CoolNamesAllTaken/scbs/solidworks/fab/enclosure_parts.3mf

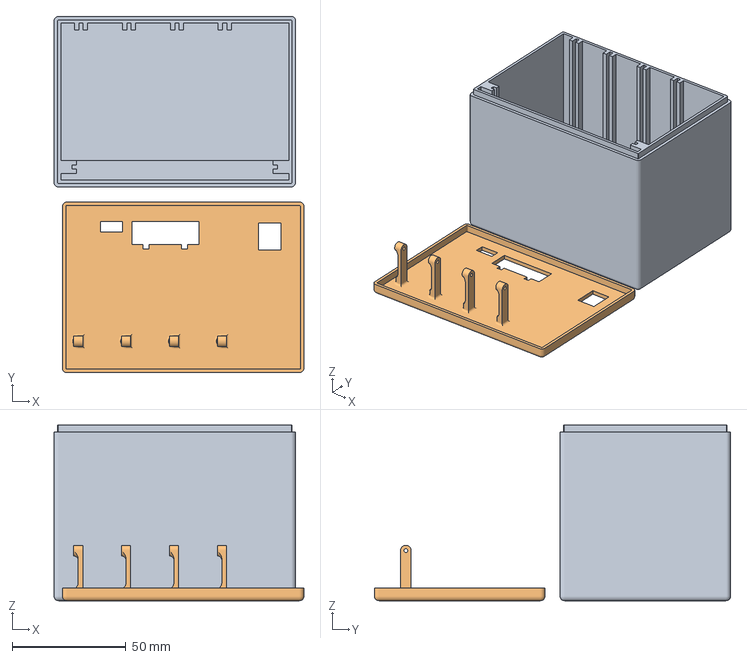
[picture p12: CAD file, 2022-12-04]
solidworks/fab/enclosure_parts.3mf
109.7 x 156.3 x 77.0 mm
enclosure_back_shell.STL
enclosure_front_panel.STL
