CoolNamesAllTaken/scbs/ltspice/cmd_pwm_tran.asc

C1: cap; 0.1µ
C2: cap; 0.1µ
Q1: npn; 2N3904
Q2: npn; 2N3904
R1: res; 10k
R2: res; 100
R3: res; 10k
R4: res; 10k
R5: res; 2k
R6: res; 10k
R7: res; 100
R8: res; 10k
V1: voltage; 5
V2: voltage; PULSE(0 3.3 0 1n 1n 10u 20u)
V3: voltage; PULSE(0 3.3 0 1n 1n 10u 20u)
Named nets: 0, 5v
.tran 10m
