CoolNamesAllTaken/scbs/ltspice/diff_amp_sim_ac.asc

C1: cap; 0.1µ
C4: cap; 0.1µ
C5: cap; 1µ
Q1: npn; 2n3904
Q2: pnp; 2n3906
R1: res; 1k
R2: res; 1k
R4: res; 10k
R5: res; 1
R6: res; 25
R7: res; 500k
R8: res; 500k
R9: res; 8.25Meg
R10: res; 8.25Meg
R11: res; 10k
R12: res; 100
R13: res; 10k
R14: res; 1
U1: UniversalOpAmp3
U2: UniversalOpAmp2
V1: voltage; 5
V2: voltage; 0; AC 1
V3: voltage; 3
Named nets: 0, 5v, out, csense, up, dn, fb, inm, hello
Q1 inverts ouptut polarity
and provides base drive for
.ac dec 1000 1m 1G
