CoolNamesAllTaken/scbs/ltspice/diff_amp_sim_offset_tran.asc

C1: cap; 1µ
C2: cap; 10n
C3: cap; 0.1µ
C4: cap; 0.1µ
Q1: npn; 2n3904
Q2: pnp; 2n2907
R1: res; 1k
R2: res; 1k
R3: res; 10k
R4: res; 2k
R5: res; 1
R6: res; 22.5
R7: res; 500k
R8: res; 500k
R9: res; 8.25Meg
R10: res; 8.25Meg
R11: res; 1
R12: res; 100
R13: res; 10k
R14: res; 2k
R15: res; 10k
U1: UniversalOpAmp2; Avol=10k GBW=10Meg Slew=18Meg
U2: UniversalOpAmp2
V1: voltage; 5
V2: voltage; SINE(2.25 2.25 100)
V3: voltage; PULSE(0 4.5 0 1n 1n 50m 100m)
V4: voltage; 3m
V5: voltage; 3m
Named nets: 0, 5v, out, csense, up, dn, cmd, hello
Q1 inverts ouptut polarity
and provides base drive for
.tran 0 100m 0 1u
