CoolNamesAllTaken/scbs/ltspice/idea_sim.asc

C1: cap; 0.1µ
R1: res; 100k
R3: res; 100
U1: LT1117
U2: UniversalOpAmp2
V1: voltage; 5
V2: voltage; PULSE(0 3.3 0 10m 0 10m 50m)
Named nets: 0, 5v, out, ref, cmd
.tran 0 10m 0 1u
V(out)-V(ref) = 1.25V
V(out) = V(ref) * (1 + R2/R1) + I(adj)*R2
