CoolNamesAllTaken/scbs/ltspice/npn_output_sim.asc

Q1: npn; 2n3904
R1: res; 10
U1: UniversalOpAmp2
V1: voltage; 5
V2: voltage; PULSE(0 4.5 0 10m 0 10m 50m)
Named nets: 0, cmd, 5v
.tran 0 10m 0 1u
V(out)-V(ref) = 1.25V
V(out) = V(ref) * (1 + R2/R1) + I(adj)*R2
