CoolNamesAllTaken/scbs/ltspice/rail_output_sim.asc

2n3906: pnp
C1: cap; 0.1µ
Q1: npn; 2n3904
R1: res; 1k
R2: res; 100
R3: res; 14.24k
R4: res; 10k
U1: UniversalOpAmp2
V1: voltage; 5
V2: voltage; SINE(1.65 1.65 10k 0 0)
Named nets: 0, cmd, 5v
.tran 0 1m 0
V(out)-V(ref) = 1.25V
V(out) = V(ref) * (1 + R2/R1) + I(adj)*R2
