CoolNamesAllTaken/scbs/ltspice/rail_output_sim_ac.asc

C1: cap; 0.1µ
C2: cap; 1p
C3: cap; 0.1µ
C4: cap; 10µ
Q1: npn; 2n3904
Q2: pnp; 2n3906
R1: res; 1k
R2: res; 1k
R3: res; 100k
R4: res; 100k
R5: res; 1
R6: res; 25
R7: res; 500k
R8: res; 500k
R9: res; 8.25Meg
R10: res; 8.25Meg
R12: res; 100
R13: res; 10k
U1: UniversalOpAmp3
U2: UniversalOpAmp2
V1: voltage; 5
V2: voltage; 0; AC 1
V3: voltage; 3
Named nets: 0, 5v, out, csense, up, dn, fb, inm
Q1 inverts ouptut polarity
and provides base drive for
.ac dec 1000 1m 10Meg
