CoolNamesAllTaken/scbs/ltspice/rail_output_sim_tran.asc

C1: cap; 1µ
C2: cap; 1p
C3: cap; 0.1µ
C4: cap; 10n
C5: cap; 10µ
Q1: npn; 2n3904
Q2: pnp; 2n3906
R1: res; 1k
R2: res; 1k
R5: res; 1
R6: res; 22.5
R7: res; 500k
R8: res; 500k
R9: res; 8.25Meg
R10: res; 8.25Meg
R11: res; 10k
R12: res; 100
U1: UniversalOpAmp2; Avol=1Meg GBW=10Meg Slew=18Meg
U2: UniversalOpAmp2
V1: voltage; 5
V2: voltage; SINE(2.25 2.25 100)
Named nets: 0, 5v, out, csense, up, dn, cmd
Q1 inverts ouptut polarity
and provides base drive for
.tran 0 100m 0 1u
